ElectroDrome/lab-tool-dekade-1/decade1.kicad_sch

## KiCad design decade1.kicad_sch (2025-07-25, last stored version)

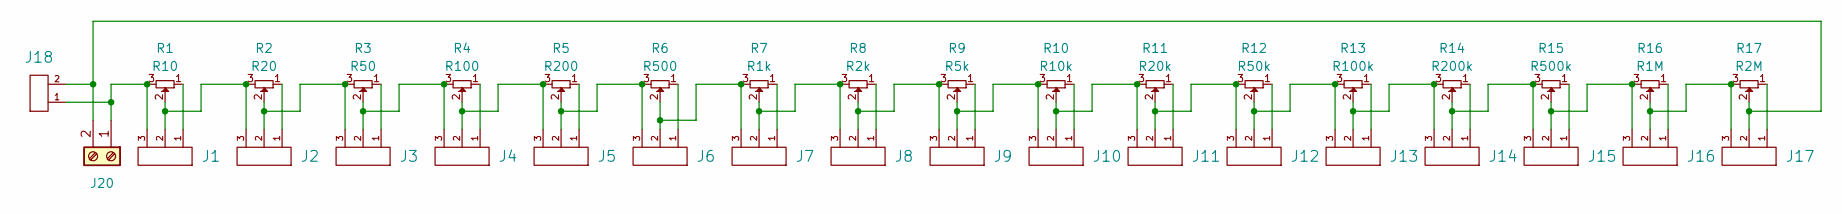
[picture p5: schematic decade1.kicad_sch]

Parts:
J1, J2, J3, J4, J5, J6, J7, J8, J9, J10, J11, J12, J13, J14, J15, J16, J17: PinHeader_1x03_P2.54mm_Vertical
J18: PinHeader_1x02_P2.54mm_Vertical
J20: TerminalBlock_Phoenix_MKDS-3-2-5.08_1x02_P5.08mm_Horizontal
R1: R10; Potentiometer_Bourns_3296W_Vertical
R2: R20; Potentiometer_Bourns_3296W_Vertical
R3: R50; Potentiometer_Bourns_3296W_Vertical
R4: R100; Potentiometer_Bourns_3296W_Vertical
R5: R200; Potentiometer_Bourns_3296W_Vertical
R6: R500; Potentiometer_Bourns_3296W_Vertical
R7: R1k; Potentiometer_Bourns_3296W_Vertical
R8: R2k; Potentiometer_Bourns_3296W_Vertical
R9: R5k; Potentiometer_Bourns_3296W_Vertical
R10: R10k; Potentiometer_Bourns_3296W_Vertical
R11: R20k; Potentiometer_Bourns_3296W_Vertical
R12: R50k; Potentiometer_Bourns_3296W_Vertical
R13: R100k; Potentiometer_Bourns_3296W_Vertical
R14: R200k; Potentiometer_Bourns_3296W_Vertical
R15: R500k; Potentiometer_Bourns_3296W_Vertical
R16: R1M; Potentiometer_Bourns_3296W_Vertical
R17: R2M; Potentiometer_Bourns_3296W_Vertical

Connections:
unnamed: J1.1, R1.1
unnamed: J1.2, J2.3, R1.2, R2.3
unnamed: J1.3, J18.1, J20.1, R1.3
unnamed: J2.1, R2.1
unnamed: J2.2, J3.3, R2.2, R3.3
unnamed: J3.1, R3.1
unnamed: J3.2, J4.3, R3.2, R4.3
unnamed: J4.1, R4.1
unnamed: J4.2, J5.3, R4.2, R5.3
unnamed: J5.1, R5.1
unnamed: J5.2, J6.3, R5.2, R6.3
unnamed: J6.1, R6.1
unnamed: J6.2, J7.3, R6.2, R7.3
unnamed: J7.1, R7.1
unnamed: J7.2, J8.3, R7.2, R8.3
unnamed: J8.1, R8.1
unnamed: J8.2, J9.3, R8.2, R9.3
unnamed: J9.1, R9.1
unnamed: J10.1, R10.1
unnamed: J10.2, J11.3, R10.2, R11.3
unnamed: J9.2, J10.3, R9.2, R10.3
unnamed: J11.1, R11.1
unnamed: J11.2, J12.3, R11.2, R12.3
unnamed: J12.1, R12.1
unnamed: J12.2, J13.3, R12.2, R13.3
unnamed: J13.1, R13.1
unnamed: J13.2, J14.3, R13.2, R14.3
unnamed: J14.1, R14.1
unnamed: J14.2, J15.3, R14.2, R15.3
unnamed: J15.1, R15.1
unnamed: J15.2, J16.3, R15.2, R16.3
unnamed: J16.1, R16.1
unnamed: J16.2, J17.3, R16.2, R17.3
unnamed: J17.1, R17.1
unnamed: J17.2, J18.2, J20.2, R17.2
